Cryochasm/christmas-tree-disco-hw/PCB/microcontroller.sch

## KiCad design PCB/microcontroller.sch (2018-01-05)

Schematic: microcontroller.sch

Parts:
H2, H4: 2x10 HEADER; 2x10_header_3d; MPN 0015912200
U1: DEV_KIT_EK-TM4C123GXL; MPN EK-TM4C123GXL
