Cryochasm/christmas-tree-disco-hw/PCB/rgb_led.sch

## KiCad design PCB/rgb_led.sch (2018-01-05)

Schematic: rgb_led.sch

Parts:
C4: 0.1u; SMD-0805; MPN CL21B104KACWPNC
D0: RGB LED; T-1_5mm; MPN WP154A4SEJ3VBDZGW/CA
