Cryochasm/christmas-tree-disco-hw/PCB/rgb_led_array.sch

## KiCad design PCB/rgb_led_array.sch (2018-01-05)

Schematic: rgb_led_array.sch

Parts:
C8: 0.1u; SMD-0805; MPN CL21B104KACWPNC
C16: 10u; SMD-TANT-1206; MPN F931A106KAA
D8: AAA3528SEEZGKQBKS; PLCC-4-3.5x2.8; MPN AAA3528SEEZGKQBKS
U2: TLC5955DCA; HTSSOP-56_14x6.1; MPN TLC5955DCAR
