Cryochasm/christmas-tree-disco-hw/PCB/top_sheet.sch

## KiCad design PCB/top_sheet.sch (2018-01-05)

Schematic: top_sheet.sch

Parts:
H1: LPRocket
H3: Snow Silk Screen; snow
H7: SPFMDBC; Open_Source_HW_Logo
V2.0: www.github.com/Cryochasm; Cryochasm
